Riyas-code-tonic/EnviroSense/Images/Block Diagram.png

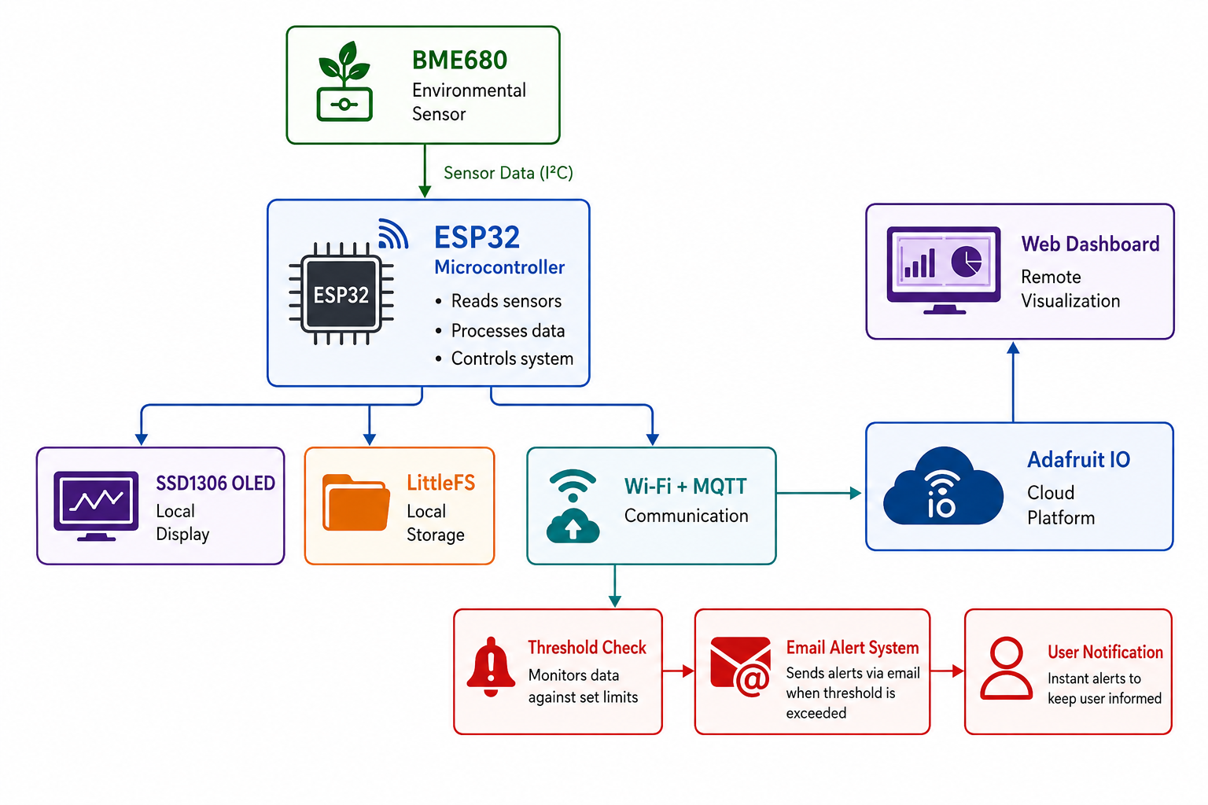
Images/Block Diagram.png
