Riyas-code-tonic/EnviroSense/Images/Dashboard/Dark mode data display.png

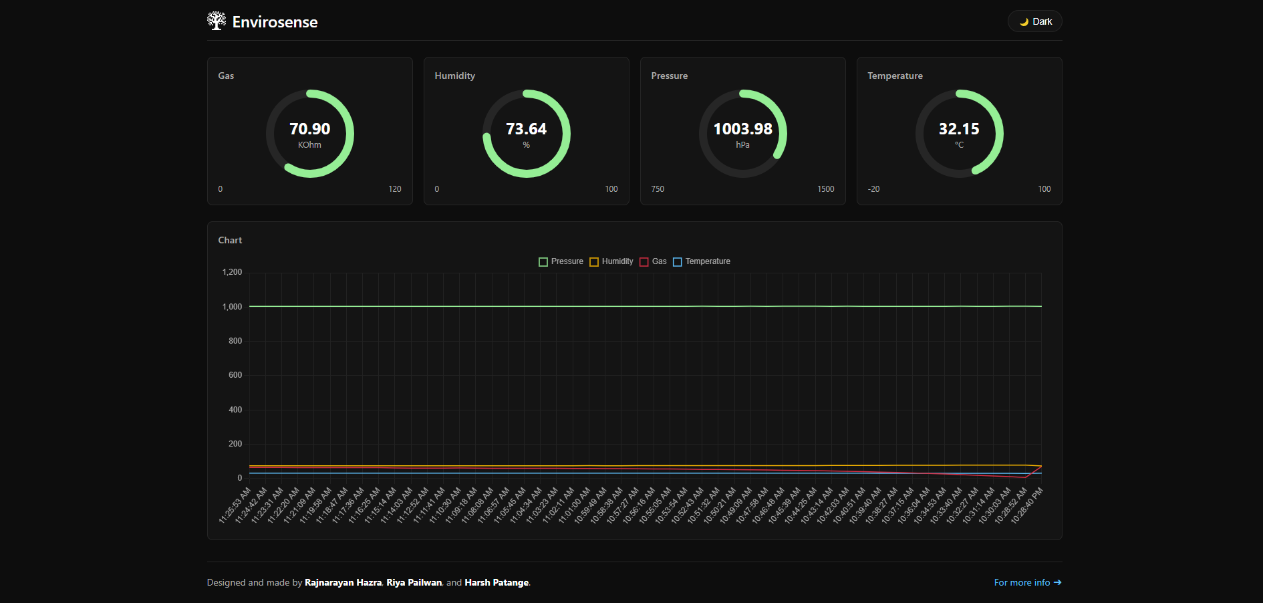
Images/Dashboard/Dark mode data display.png
