Riyas-code-tonic/EnviroSense/Images/Dashboard/html_dash_clean.png

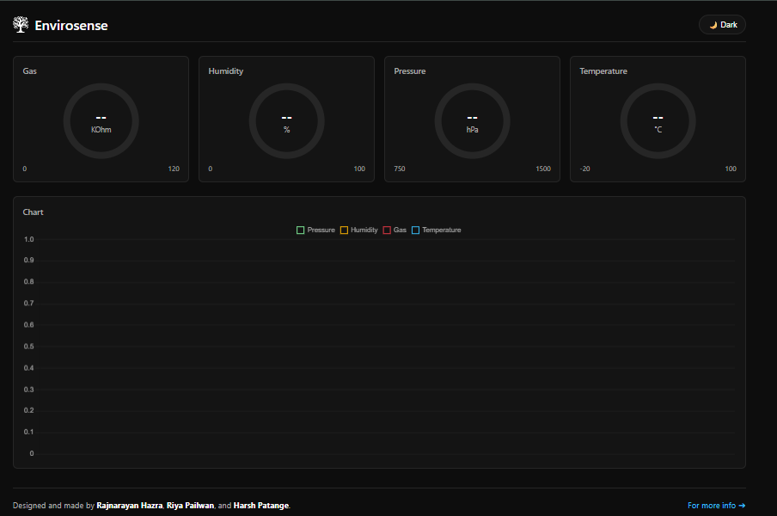
Images/Dashboard/html_dash_clean.png
