Riyas-code-tonic/EnviroSense/Images/Dashboard/Light mode data display.png

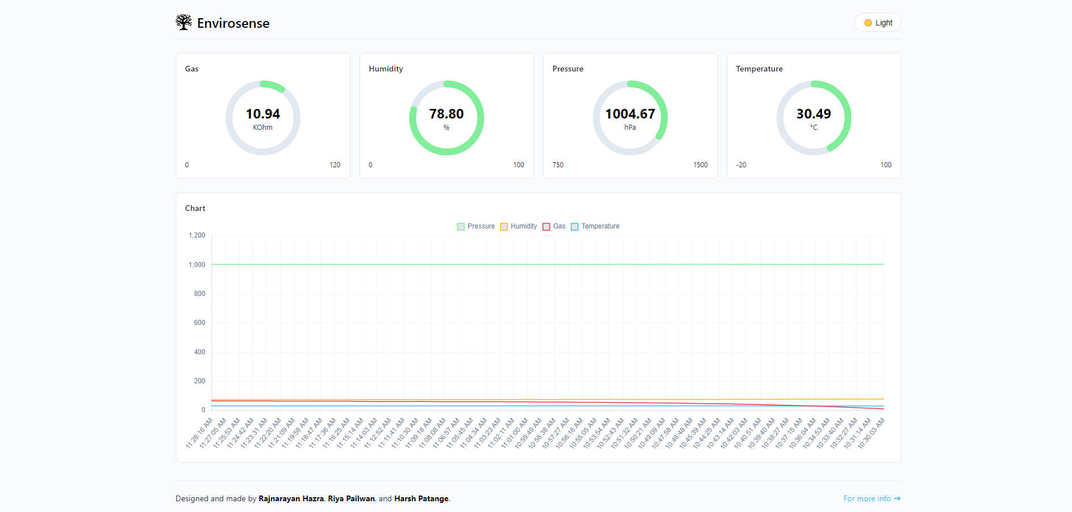
Images/Dashboard/Light mode data display.png
