Riyas-code-tonic/EnviroSense/Images/Email/Gmail.png

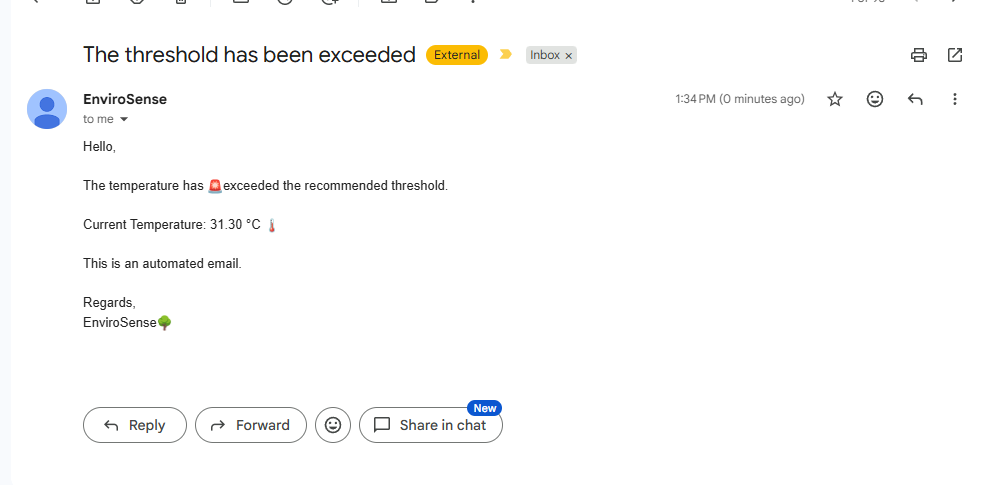
Images/Email/Gmail.png
