Riyas-code-tonic/EnviroSense/Images/Flowchart.png

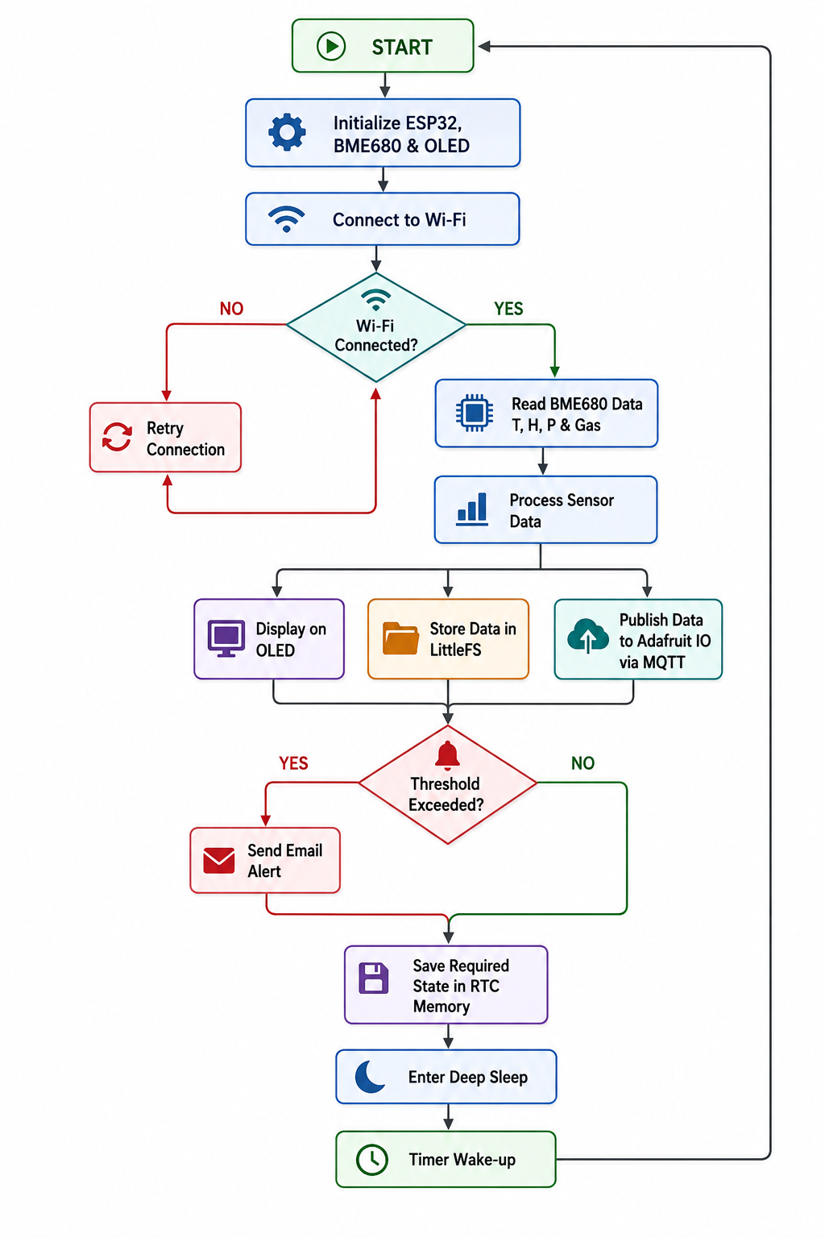
Images/Flowchart.png
