Riyas-code-tonic/EnviroSense/Images/MQTT Server/MQTT.png

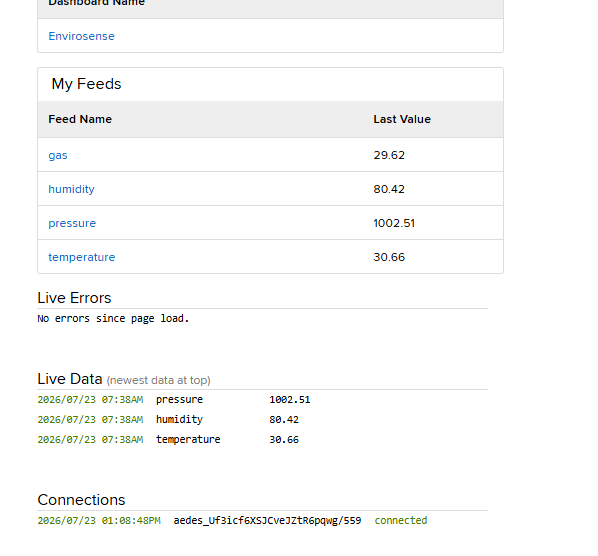
Images/MQTT Server/MQTT.png
