Riyas-code-tonic/EnviroSense/Images/PCB/PCB1.jpeg

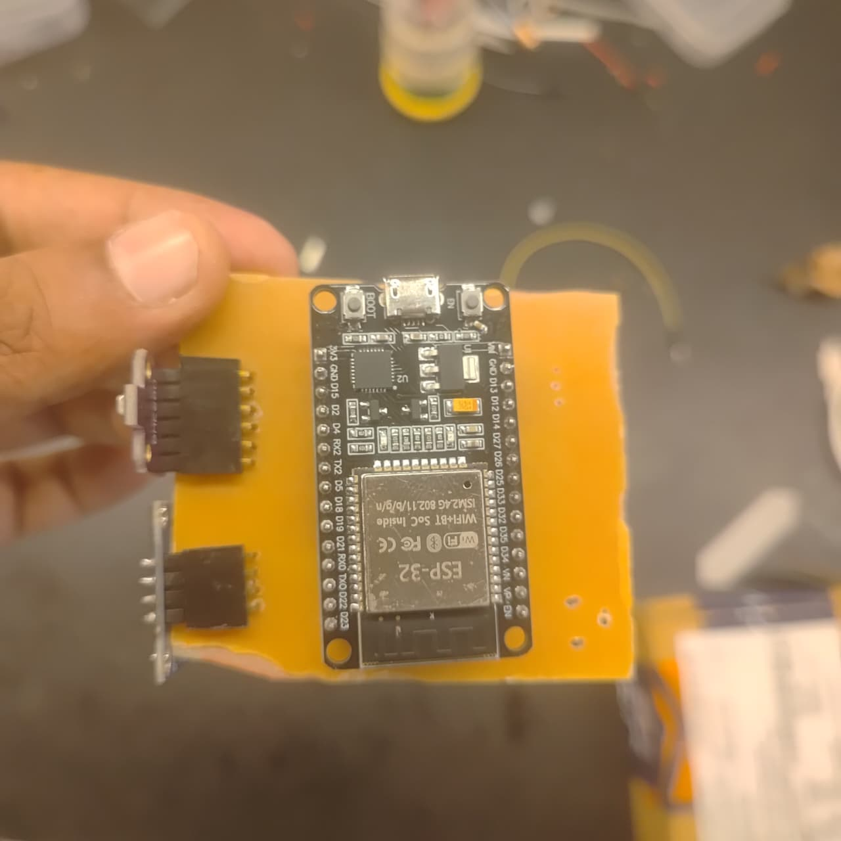
Images/PCB/PCB1.jpeg
