Riyas-code-tonic/EnviroSense/Images/PCB/PCB2.jpeg

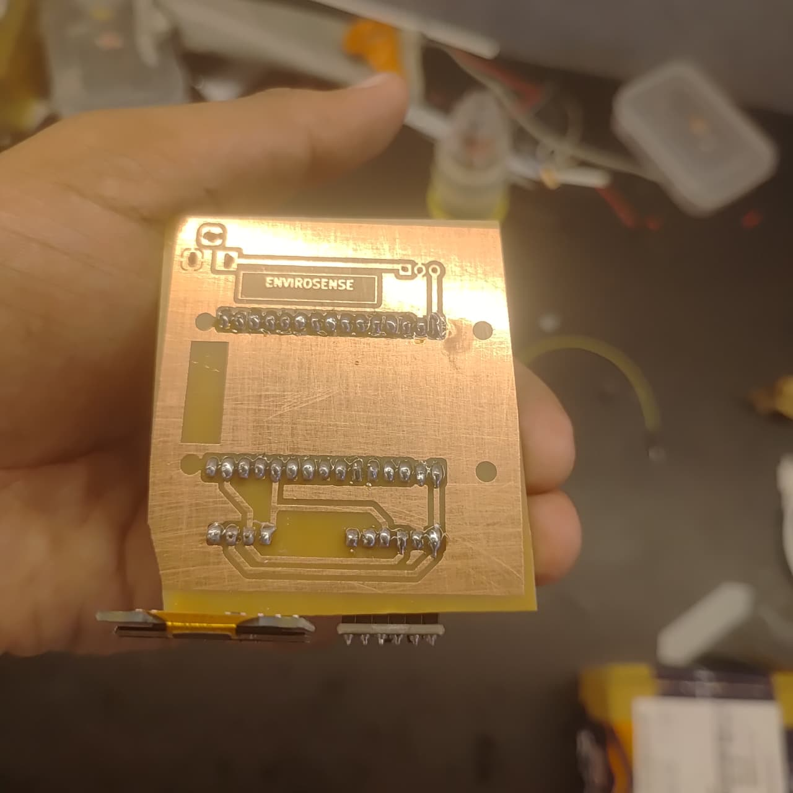
Images/PCB/PCB2.jpeg
