Riyas-code-tonic/EnviroSense/Images/Sensor/BME680 sensor.png

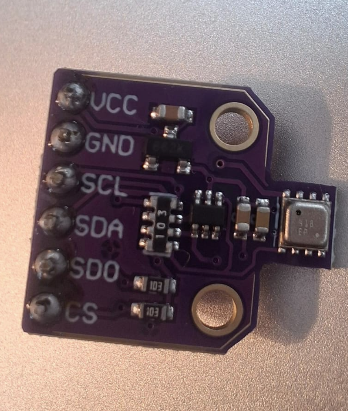
Images/Sensor/BME680 sensor.png
