Riyas-code-tonic/EnviroSense/Images/Serial Monitor/Real Time Data.png

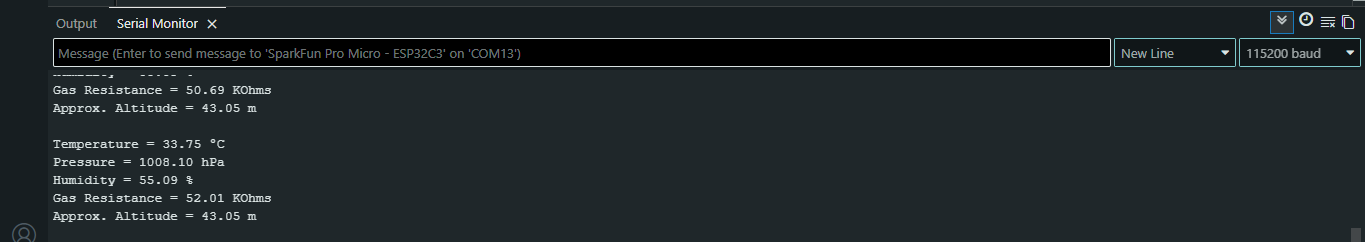
Images/Serial Monitor/Real Time Data.png
