Riyas-code-tonic/EnviroSense/Images/Serial Monitor/Wifi connection and display temperature.png

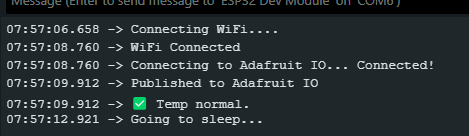
Images/Serial Monitor/Wifi connection and display temperature.png
